DIYSynthMNL/Eurorack-PT2399-Delay/kicad/Eurorack-PT2399-Delay.kicad_pcb

## KiCad design cuarenta/cuarenta.kicad_pcb

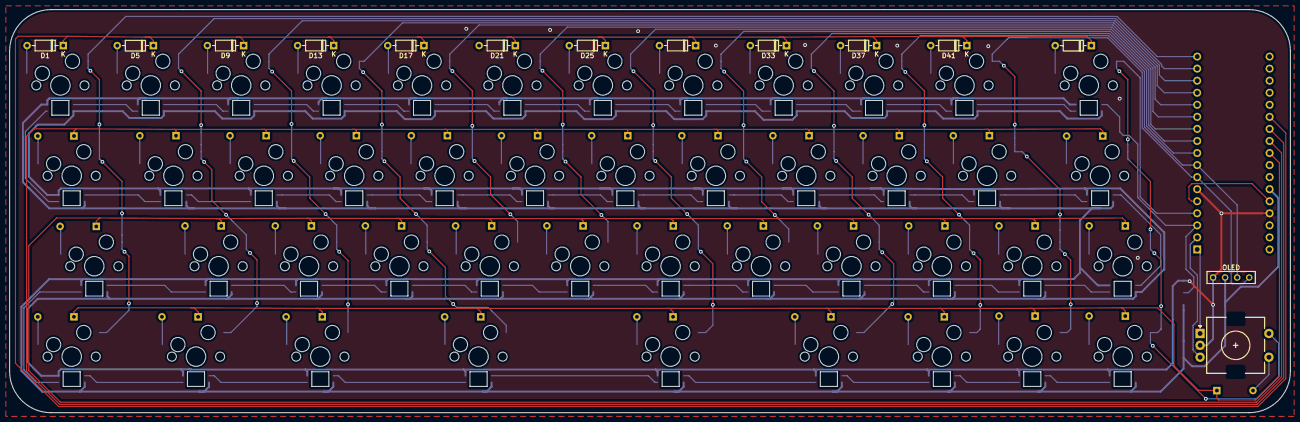
[picture p6: board cuarenta.kicad_pcb from above]

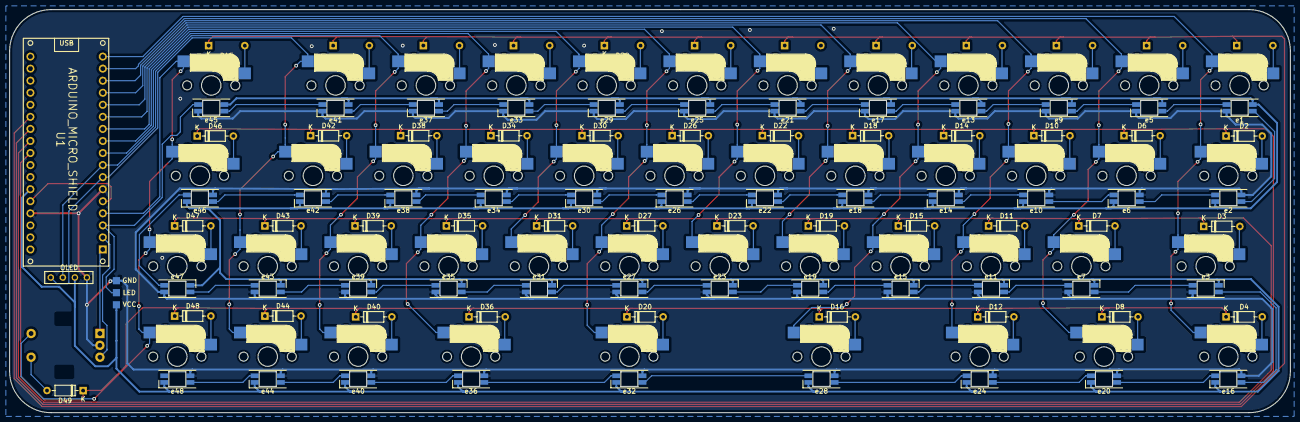
[picture p7: board cuarenta.kicad_pcb from below]

Board: 2 copper layers, 269.9 x 84.9 mm, 140 parts (81 on the bottom side), 111 nets.

Parts:
D1, D2, D3, D4, D5, D6, D7, D8, D9, D10, D11, D12, D13, D14, D15, D16, D17, D18, D19, D20, D21, D22, D23, D25, D26, D27, D29, D30, D31, D33, D34, D35, D36, D37, D38, D39, D40, D41, D42, D43, D44, D45, D46, D47, D48, D49: 1N4148; D_DO-35_SOD27_P7.62mm_Horizontal
J1: LED; StripLED_1side
OL1: OLED
SW1, SW2, SW3, SW4, SW5, SW6, SW7, SW8, SW9, SW10, SW11, SW12, SW13, SW14, SW15, SW16, SW17, SW18, SW19, SW20, SW21, SW22, SW23, SW25, SW26, SW27, SW29, SW30, SW31, SW33, SW34, SW35, SW36, SW37, SW38, SW39, SW40, SW41, SW42, SW43, SW44, SW45, SW46, SW47, SW48: SW_Push; CherryMX_Hotswap
SW49: Rotary_Encoder_Switch; RotaryEncoder_EC11
U1: ARDUINO_MICRO_SHIELD
e1, e2, e3, e5, e6, e7, e9, e10, e11, e13, e14, e15, e16, e17, e18, e19, e20, e21, e22, e23, e24, e25, e26, e27, e28, e29, e30, e31, e32, e33, e34, e35, e36, e37, e38, e39, e40, e41, e42, e43, e44, e45, e46, e47, e48: e; YS-SK6812MINI-E_2

Connections:
Col0: SW1.2, SW2.2, SW3.2, SW4.2, U1.12
Col1: SW5.2, SW6.2, SW7.2, SW8.2, U1.11
Col2: SW9.2, SW10.2, SW11.2, SW12.2, U1.10
Col3: SW13.2, SW14.2, SW15.2, SW16.2, U1.9
Col4: SW17.2, SW18.2, SW19.2, U1.8
Col5: SW21.2, SW22.2, SW23.2, U1.7
Col6: SW20.2, SW25.2, SW26.2, SW27.2, U1.6
Col7: SW29.2, SW30.2, SW31.2, U1.5
Col8: SW33.2, SW34.2, SW35.2, SW36.2, U1.4
Col9: OL1.3, SW37.2, SW38.2, SW39.2, SW40.2, U1.3
Col10: OL1.4, SW41.2, SW42.2, SW43.2, SW44.2, U1.2
Col11: SW45.2, SW46.2, SW47.2, SW48.2, SW49.S2, U1.RX
GND: J1.3, OL1.1, SW49.C, U1.GND, e1.3, e2.1, e3.1, e5.3, e6.1, e7.1, e9.3, e10.1, e11.1, e13.3, e14.1, e15.1, e16.1, e17.3, e18.1, e19.1, e20.1, e21.3, e22.1, e23.1, e24.1, e25.3, e26.1, e27.1, e28.1, e29.3, e30.1, e31.1, e32.1, e33.3, e34.1, e35.1, e36.1, e37.3, e38.1, e39.1, e40.1, e41.3, e42.1, e43.1, e44.1, e45.3, e46.1, e47.1, e48.1
LED: J1.2, U1.TX, e45.4
unnamed: D1.2, SW1.1
unnamed: D2.2, SW2.1
unnamed: D3.2, SW3.1
unnamed: D4.2, SW4.1
unnamed: D5.2, SW5.1
unnamed: D6.2, SW6.1
unnamed: D7.2, SW7.1
unnamed: D8.2, SW8.1
unnamed: D9.2, SW9.1
unnamed: D10.2, SW10.1
unnamed: D11.2, SW11.1
unnamed: D12.2, SW12.1
unnamed: D13.2, SW13.1
unnamed: D14.2, SW14.1
unnamed: D15.2, SW15.1
unnamed: D16.2, SW16.1
unnamed: D17.2, SW17.1
unnamed: D18.2, SW18.1
unnamed: D19.2, SW19.1
unnamed: D20.2, SW20.1
unnamed: D21.2, SW21.1
unnamed: D22.2, SW22.1
unnamed: D23.2, SW23.1
unnamed: D25.2, SW25.1
unnamed: D26.2, SW26.1
unnamed: D27.2, SW27.1
unnamed: D29.2, SW29.1
unnamed: D30.2, SW30.1
unnamed: D31.2, SW31.1
unnamed: D33.2, SW33.1
unnamed: D34.2, SW34.1
unnamed: D35.2, SW35.1
unnamed: D36.2, SW36.1
unnamed: D37.2, SW37.1
unnamed: D38.2, SW38.1
unnamed: D39.2, SW39.1
unnamed: D40.2, SW40.1
unnamed: D41.2, SW41.1
unnamed: D42.2, SW42.1
unnamed: D43.2, SW43.1
unnamed: D44.2, SW44.1
unnamed: D45.2, SW45.1
unnamed: D46.2, SW46.1
unnamed: D47.2, SW47.1
unnamed: D48.2, SW48.1
unnamed: D49.2, SW49.S1
unnamed: e1.2, e2.2
unnamed: e1.4, e5.2
unnamed: e2.4, e6.2
unnamed: e3.2, e7.4
unnamed: e5.4, e9.2
unnamed: e6.4, e10.2
unnamed: e10.4, e14.2
unnamed: e11.2, e15.4
unnamed: e7.2, e11.4
unnamed: e9.4, e13.2
unnamed: e13.4, e17.2
unnamed: e14.4, e18.2
unnamed: e15.2, e19.4
unnamed: e3.4, e16.2
unnamed: e16.4, e20.2
unnamed: e17.4, e21.2
unnamed: e18.4, e22.2
unnamed: e19.2, e23.4
unnamed: e20.4, e24.2
unnamed: e21.4, e25.2
unnamed: e22.4, e26.2
unnamed: e23.2, e27.4
unnamed: e24.4, e28.2
unnamed: e25.4, e29.2
unnamed: e26.4, e30.2
unnamed: e27.2, e31.4
unnamed: e28.4, e32.2
unnamed: e29.4, e33.2
unnamed: e30.4, e34.2
unnamed: e31.2, e35.4
unnamed: e32.4, e36.2
unnamed: e33.4, e37.2
unnamed: e34.4, e38.2
unnamed: e35.2, e39.4
unnamed: e36.4, e40.2
unnamed: e37.4, e41.2
unnamed: e38.4, e42.2
unnamed: e39.2, e43.4
unnamed: e40.4, e44.2
unnamed: e41.4, e45.2
unnamed: e42.4, e46.2
unnamed: e43.2, e47.4
unnamed: e44.4, e48.2
unnamed: e46.4, e47.2
Row0: D1.1, D5.1, D9.1, D13.1, D17.1, D21.1, D25.1, D29.1, D33.1, D37.1, D41.1, D45.1, U1.A2
Row1: D2.1, D6.1, D10.1, D14.1, D18.1, D22.1, D26.1, D30.1, D34.1, D38.1, D42.1, D46.1, U1.A3
Row2: D3.1, D7.1, D11.1, D15.1, D19.1, D23.1, D27.1, D31.1, D35.1, D39.1, D43.1, D47.1, U1.A4
Row3: D4.1, D8.1, D12.1, D16.1, D20.1, D36.1, D40.1, D44.1, D48.1, D49.1, U1.A5
VCC: J1.1, OL1.2, U1.5V, e1.1, e2.3, e3.3, e5.1, e6.3, e7.3, e9.1, e10.3, e11.3, e13.1, e14.3, e15.3, e16.3, e17.1, e18.3, e19.3, e20.3, e21.1, e22.3, e23.3, e24.3, e25.1, e26.3, e27.3, e28.3, e29.1, e30.3, e31.3, e32.3, e33.1, e34.3, e35.3, e36.3, e37.1, e38.3, e39.3, e40.3, e41.1, e42.3, e43.3, e44.3, e45.1, e46.3, e47.3, e48.3
en1: SW49.B, U1.SS
en2: SW49.A, U1.MO
